h2horn/thunder/src/config.h

/*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
 * You should have received a copy of the GNU General Public License
 * along with this program; if not, write to the Free Software
 * Foundation, Inc., 51 Franklin Street, Fifth Floor Boston, MA 02110-1301,  USA
 */

// This is ATXM2.config.h

#ifndef CONFIG_H
	#define CONFIG_H

	#define F_CPU 32000000UL

	// Define network config if DHCP fails these are the values that will be used as a fallback or when DHCP disable
	#define MYIP			IPDOT( 10l, 0l, 42l, 223l )
	#define NETMASK 		IPDOT( 255l, 255l, 255l, 0l )
	#define GATEWAY			IPDOT( 10l, 0l, 42l, 1l )
	#define DNSSERVER		IPDOT( 10l, 0l, 42l, 1l )

	// define external XTAL frequency. if not defined, internal RC osc will be used
	#define EXT_XTAL		16000000UL
	#define EXT_XTAL_MULTI	2

	// aktiviert TCP
	// #define TCP
	#ifdef TCP
		// empfÃ¤ngt und sendet RTT im TCP-Header mit um die Performace zu verbessern
		#define TCP_RTT
		// Erlaubt den Stack ein Packet zwischen zu speichern wenn sie in der Falschen reihenfolge kommen
		#define TCP_with_unsortseq
		// Beschleunigt TCP in Verbindung mit Windows
		#define TCP_delayed_ack
	#endif

	// aktiviert UDP
	#define UDP
	
	#ifdef UDP
		// aktiviert DHCP, dazu muss UDP aktiv sein
		// Wenn DHCP nicht benutzt wird kann die statische IP in
		// system/net/ip.c geÃ¤ndert werden
		#define DHCP
		// Versucht bei einem Fehlversuch von DHCP die IP aus der Config zu lesen, sonst die in ip.c
		#define READ_CONFIG
		// aktiviert DNS, dazu muss UDP aktiv sein
		// #define DNS
		// aktiviert NTP, dazu muss UDP aktiv sein
		// #define NTP
	#endif

	#ifdef TCP

		// aktiviert DynDNS
		#ifdef DNS
			#define DYNDNS
		#endif

		#define SHELL
		#ifdef SHELL
			// aktiviert den Telnet-Server, dazu muss TCP aktiv sein
			#define TELNETSERVER
		#endif

		// aktiviert den HTTP-Server, dazu muss TCP aktiv sein
		#define HTTPSERVER
		#ifdef HTTPSERVER
			#if defined(MMC)// holt Dateien vom HTTP-Server nur von der MMC
				#define HTTP_FILES_FROM_MMC
			#endif
			// aktiviert die Stats per Webinterface
			#define HTTPSERVER_STATS
			// aktiviert die Konfiguration per Webinterface
			#define HTTPSERVER_NETCONFIG

			// aktiviert das System-MenÃ¼ per Webinterface
			#define HTTPSERVER_SYSTEM
			#ifdef HTTPSERVER_SYSTEM
				#ifdef DYNDNS
					#define HTTPSERVER_DYNDNS
				#endif
				// aktiviert twitter per Webinterface
				#if defined(TWITTER)
					#define HTTPSERVER_TWITTER
				#endif
				// aktiviert ntp per Webinterface
				#if defined(NTP)
					#define HTTPSERVER_NTP
				#endif
				// aktiviert eemem per Webinterface
				#define HTTPSERVER_EEMEM
				// aktiviert reset per Webinterface
				#define HTTPSERVER_CRON
				// aktiviert reset per Webinterface
				#define HTTPSERVER_RESET
				// aktiviert HAL info per Webinterface
				#define HTTPSERVER_HAL
			#endif

			// aktiviert IO auf dem Webinterface
			#define HTTPSERVER_IO
			#ifdef HTTPSERVER_IO
				// aktiviert ADC auf dem Webinterface
				#ifdef ANALOG
					#define HTTPSERVER_ANALOG
				#endif
				// aktiviert GPIO auf dem Webinterface
				#ifdef DIGITAL_IO
					#define HTTPSERVER_DIGITAL_IO
				#endif
				// aktiviert 1-Wire auf dem Webinterface
				#ifdef ONEWIRE
					#define HTTPSERVER_ONEWIRE
				#endif
				// aktiviert TWI auf dem Webinterface
				#ifdef TWI
					#define HTTPSERVER_TWI
				#endif
				// aktivert Impulsecounter per Webinterface
				#ifdef IMPULSCOUNTER
					#define HTTPSERVER_IMPULSECOUNTER
				#endif
			#endif
		#endif
	#endif

#endif /* ATXM2_CONFIG_H */
